konstantindenerz/sweep/gallery/sweep-bling-mx-bottom/back.png

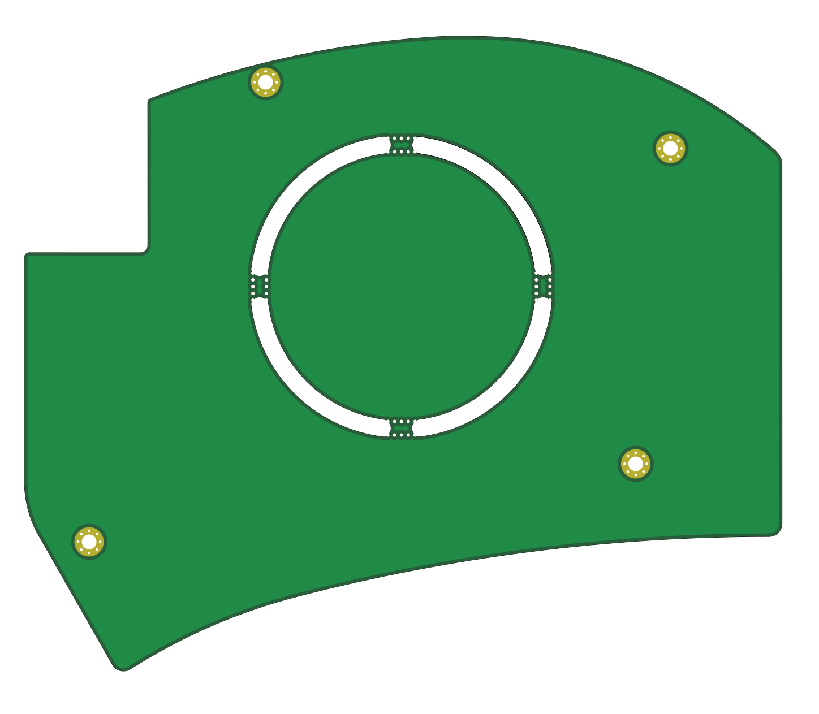
gallery/sweep-bling-mx-bottom/back.png
