konstantindenerz/sweep/gallery/sweep-bling-mx-plate/back.png

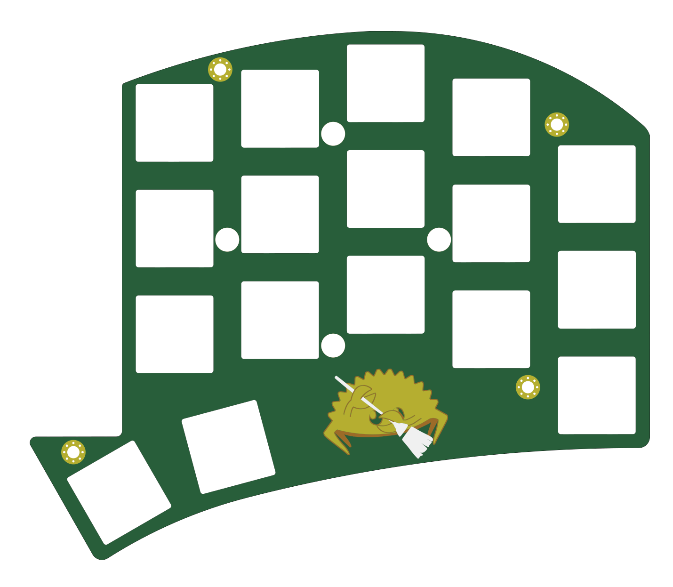
gallery/sweep-bling-mx-plate/back.png
