konstantindenerz/sweep/gallery/sweep-bling-mx-plate/front.png

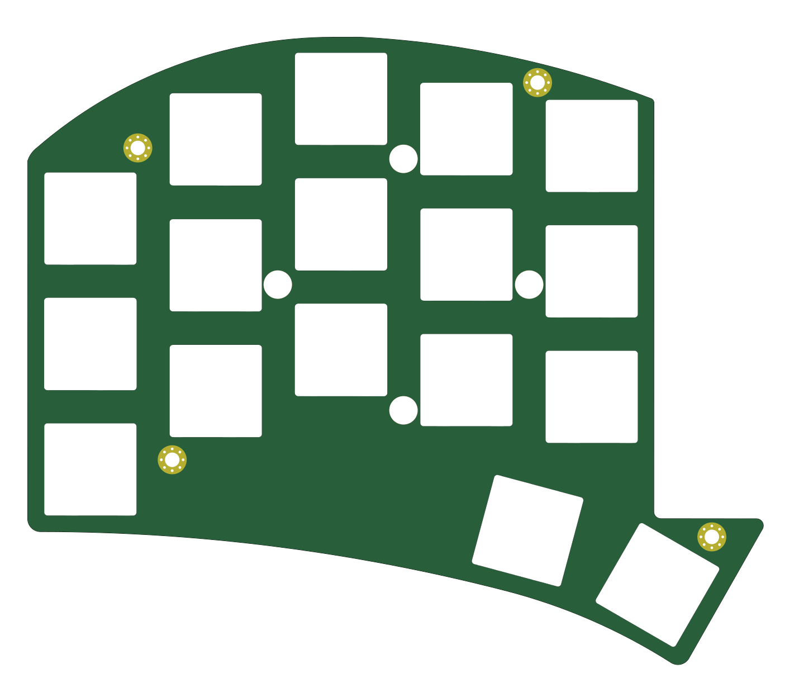
gallery/sweep-bling-mx-plate/front.png
