konstantindenerz/sweep/gallery/sweep-bling-mx/front.png

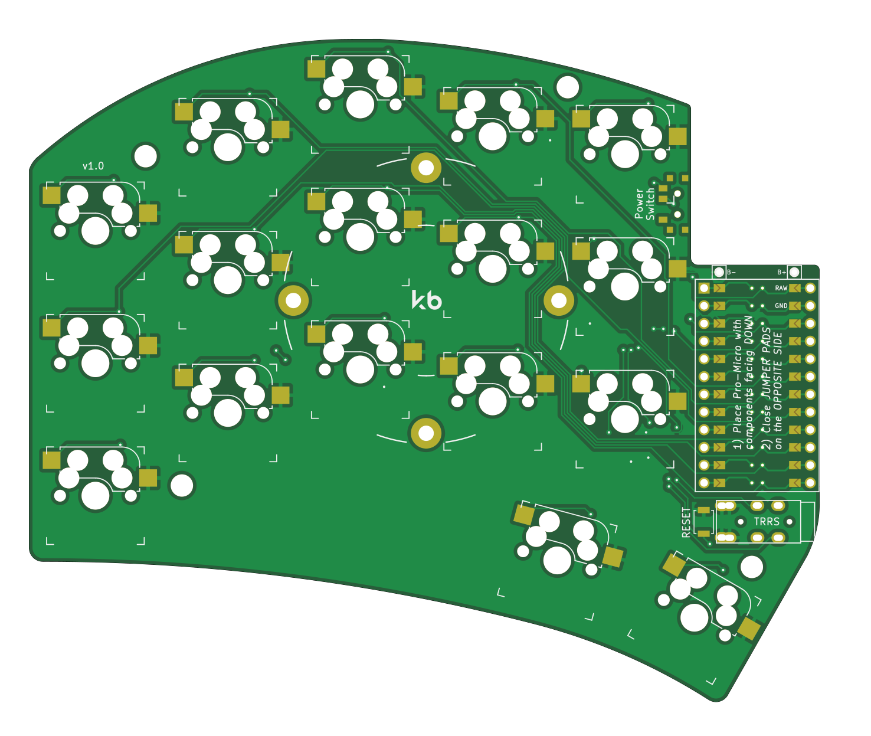
gallery/sweep-bling-mx/front.png
