konstantindenerz/sweep/gallery/sweep-high-m/front.png

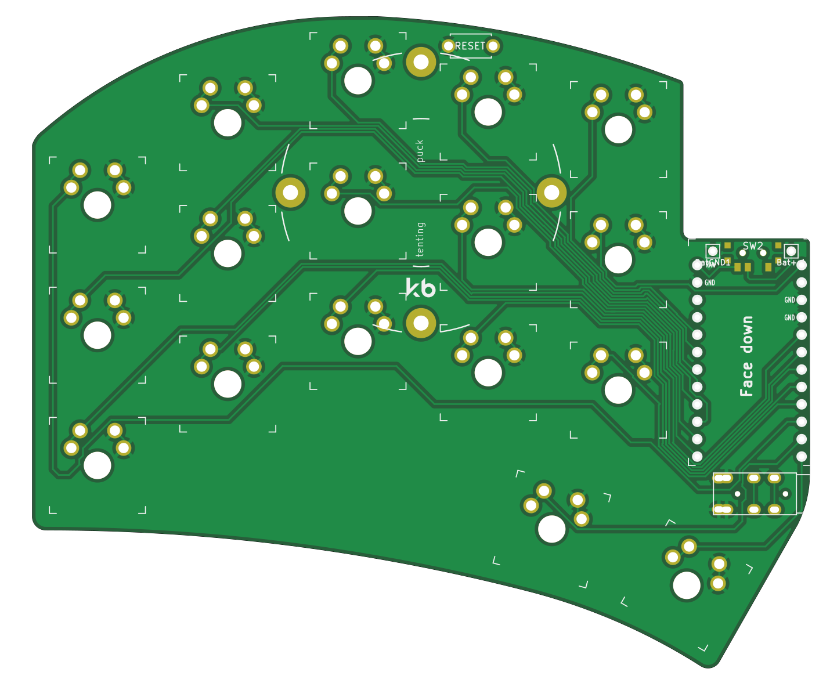
gallery/sweep-high-m/front.png
