konstantindenerz/sweep/gallery/sweepv2/back.png

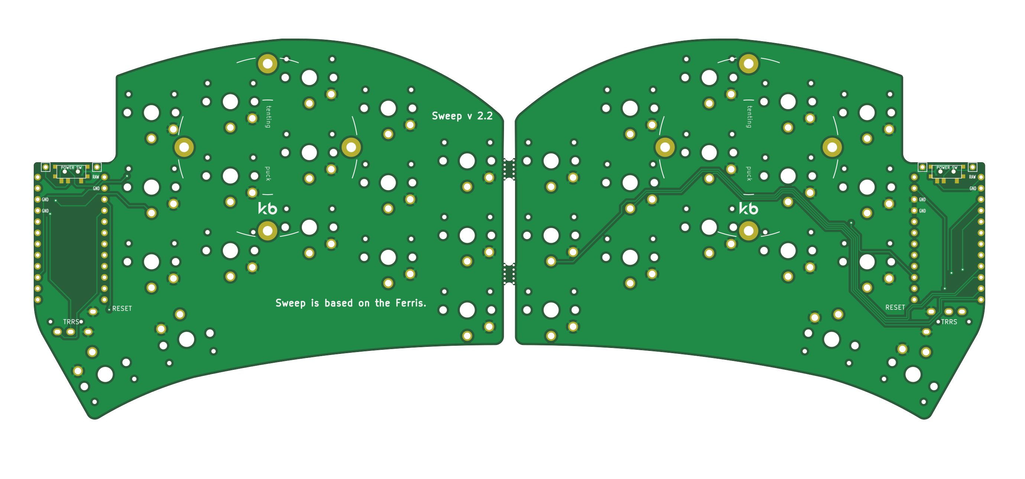
gallery/sweepv2/back.png
